Matthew-Hubbard/Plant_Monitor_Project/plant_back_end/sensors/urls.py

from django.urls import path

from . import views

urlpatterns = [
    path('', views.index, name='sensors_index'),
    path('send_data/', views.send_data, name='send_data'),
    path('get_all/<int:sensor_id>', views.sensor_data_all, name='sensor_data_all'),
]
