Matthew-Hubbard/Plant_Monitor_Project/plant_back_end/sensors/forms.py

# https://tutorial.djangogirls.org/en/django_forms/
from django import forms
from .models import Sensor_data

class Sensor_form(forms.ModelForm):

    class Meta:
        model = Sensor_data
        fields = ('sensor_id', 'temp_soil', 'temp_room', 'humidity', 'heat_index', 'moisture', 'lux', 'visible', 'ir', 'full') #timestamp set in code in views.py
